kovvalinio/Flying-unit-diagnostic-station/acqusition_data_stmf756/Core/Src/accelerometer_config.c

/*
 * accelerometer_config.c
 *
 *  Created on: Jan 31, 2023
 *      Author: kovvalinio
 */

#include "accelerometer_config.h"
#include "app_mems.h"
#include "main.h"
#include <stdio.h>

#include "iks02a1_motion_sensors.h"
#include "custom.h"
#include "math.h"




void measure_and_add(ism330dhcx_axis3bit16_t *data){


	if(HAL_I2C_Mem_Read_IT(&hi2c4, ACC_ADDRESS, ACC_AXES_ADDRESS, 1, data, 6)==HAL_OK){

	}

}
